andreapedrini01/solar-tracker-repository/Solar_Tracker/StepperLib/base_stepper.h

#ifndef __BASE_STEPPER_H__
#define __BASE_STEPPER_H__

#include <ti/devices/msp432p4xx/driverlib/driverlib.h>
#include "msp.h"

#define BASE_STEP_PIN GPIO_PIN6  // Specifica il pin per il segnale STEP
#define BASE_DIR_PIN GPIO_PIN7   // Specifica il pin per il segnale DIR

extern void init_baseStepper();
static void stepBaseMotor();
extern void moveBase(int steps);

#endif
