andreapedrini01/solar-tracker-repository/Solar_Tracker/StepperLib/top_stepper.h

#ifndef __TOP_STEPPER_H__
#define __TOP_STEPPER_H__

#include <ti/devices/msp432p4xx/driverlib/driverlib.h>
#include "msp.h"

#define TOP_STEP_PIN GPIO_PIN6  // Specifica il pin per il segnale STEP
#define TOP_DIR_PIN GPIO_PIN5   // Specifica il pin per il segnale DIR

extern void init_topStepper();
static void stepTopMotor();
extern void moveTop(int steps);

#endif
